Spo-ck/MEADE-LX200-Telescope-GOTO-Hand-Controller-Repair-Capacitor-Kondensator-Issue-solved/3D-Printing/lx2000_casetube.stl

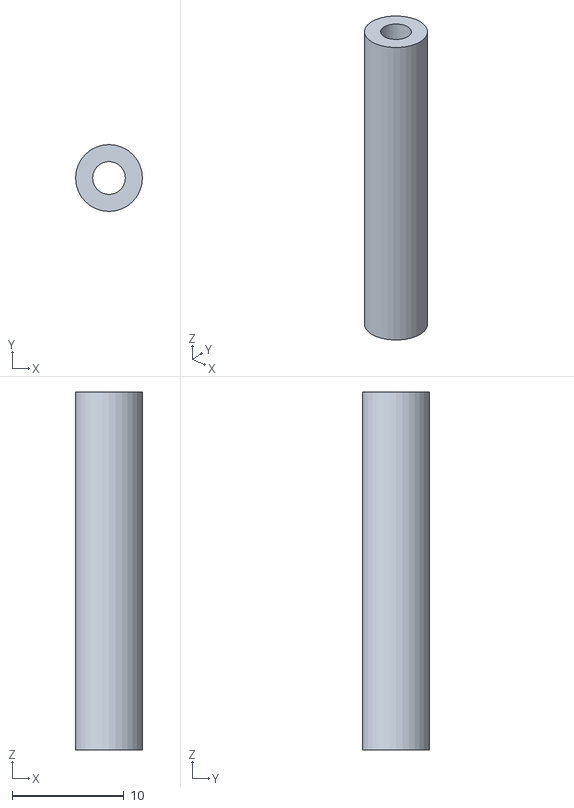
[picture p32: CAD file, 2020-09-30]
3D-Printing/lx2000_casetube.stl
6.00 x 6.00 x 32.1
