Spo-ck/MEADE-LX200-Telescope-GOTO-Hand-Controller-Repair-Capacitor-Kondensator-Issue-solved/Cable Repair/varnished wired.jpg

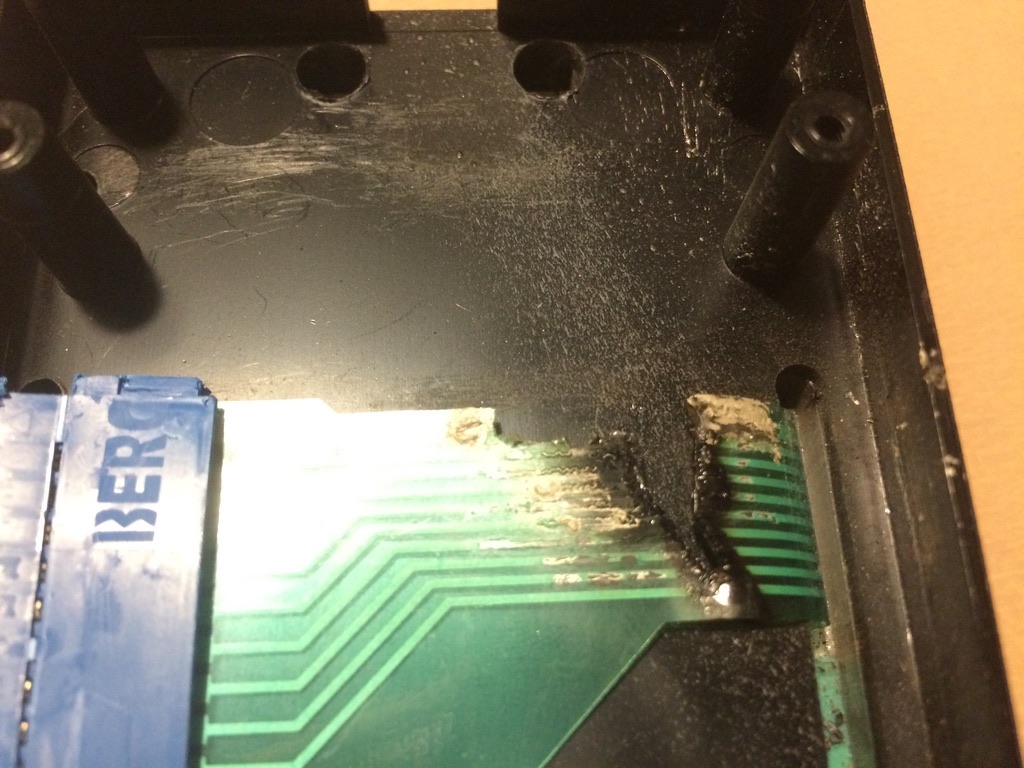
Cable Repair/varnished wired.jpg
